Altf4ah/Modified-7-Level-PUC-Inverter-for-Photovoltaic-Applications/Arduino code/code.png

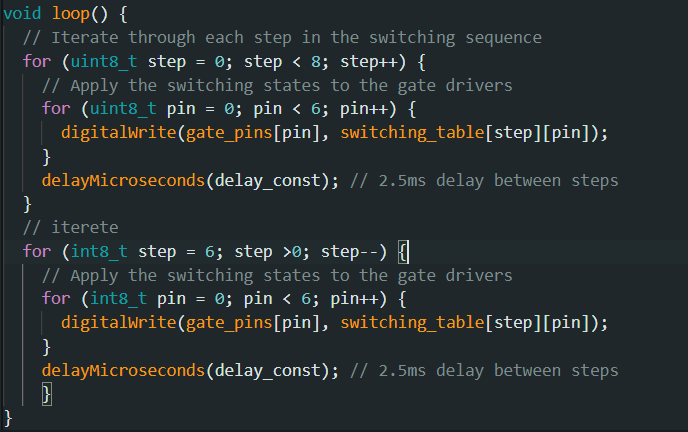
Arduino code/code.png
