Altf4ah/Modified-7-Level-PUC-Inverter-for-Photovoltaic-Applications/Arduino code/switching_table.png

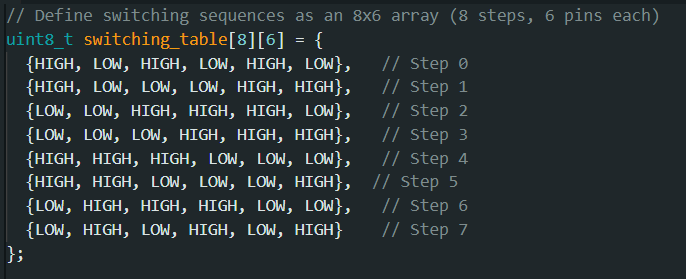
Arduino code/switching_table.png
