Altf4ah/Modified-7-Level-PUC-Inverter-for-Photovoltaic-Applications/Images/Circuit Diagrams/closedloop.jpg

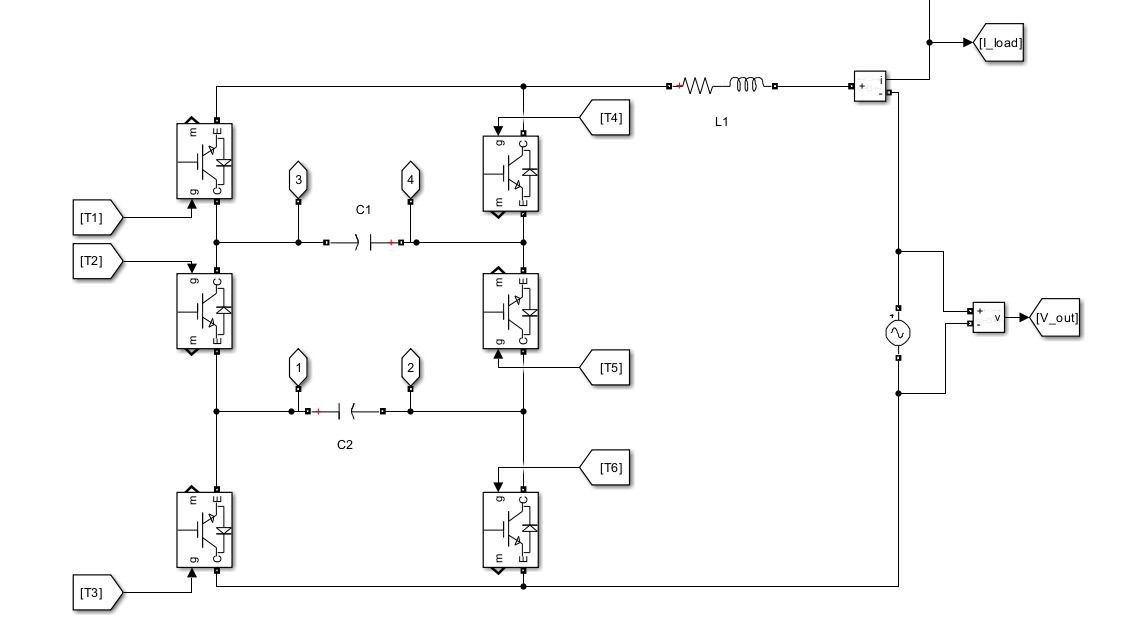
Images/Circuit Diagrams/closedloop.jpg
