Altf4ah/Modified-7-Level-PUC-Inverter-for-Photovoltaic-Applications/Images/Circuit Diagrams/driver_schematic.png

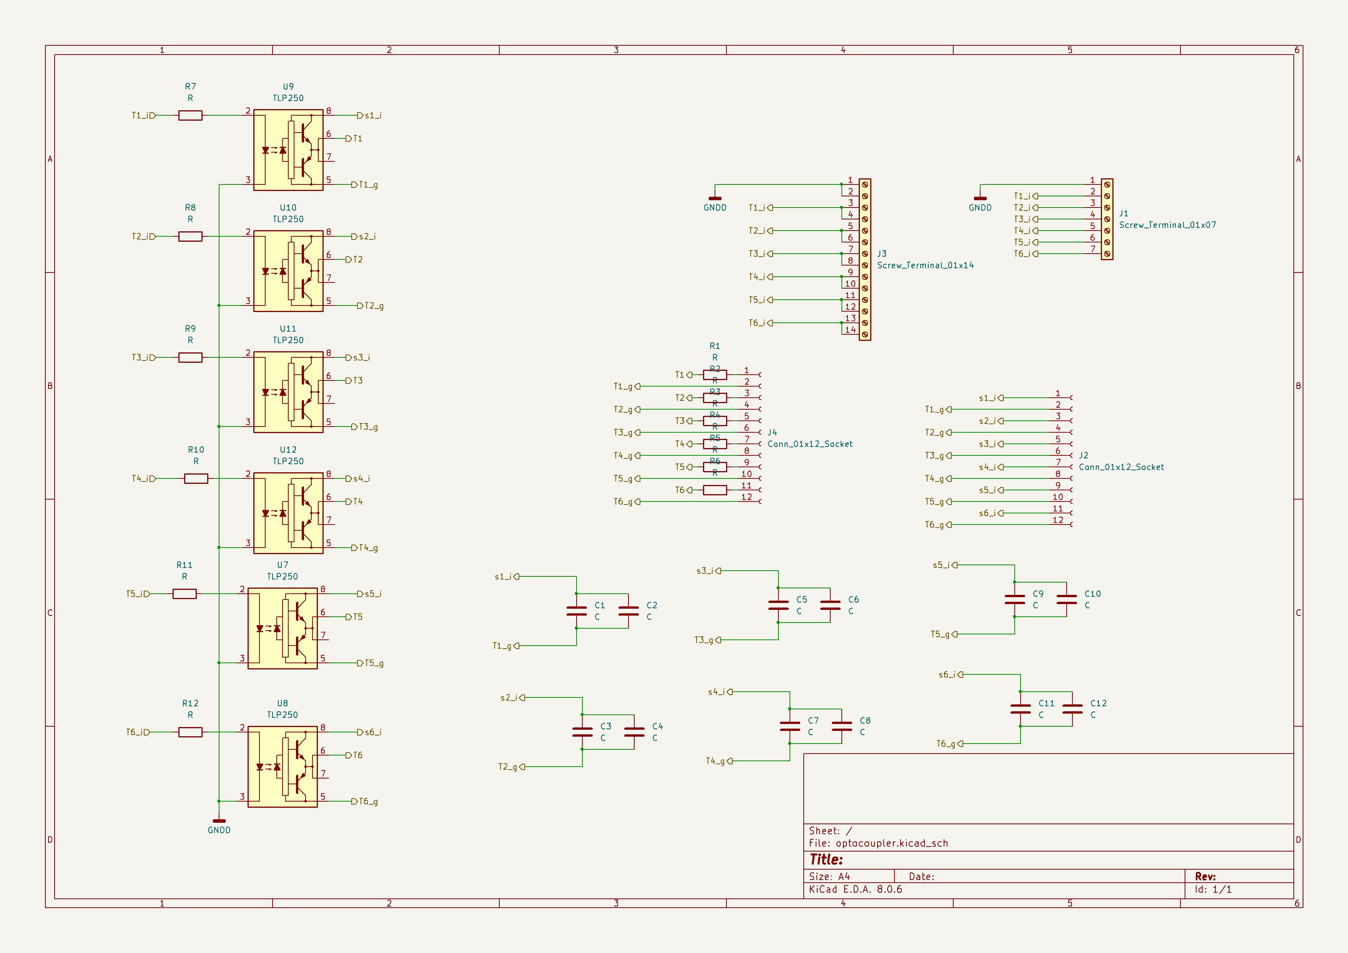
Images/Circuit Diagrams/driver_schematic.png
