Altf4ah/Modified-7-Level-PUC-Inverter-for-Photovoltaic-Applications/Images/Circuit Diagrams/Etching/etching1.jpg

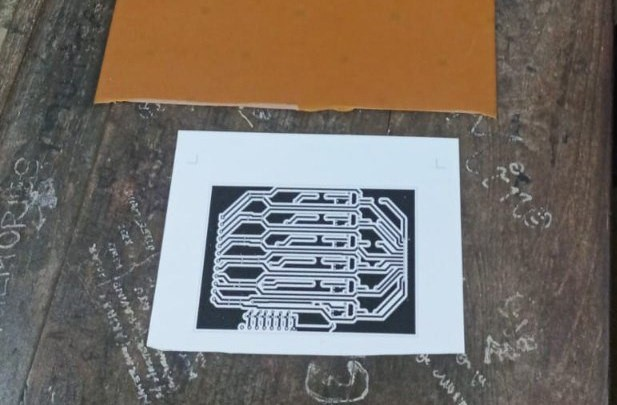
Images/Circuit Diagrams/Etching/etching1.jpg
