Altf4ah/Modified-7-Level-PUC-Inverter-for-Photovoltaic-Applications/Images/Circuit Diagrams/Etching/etching3.jpg

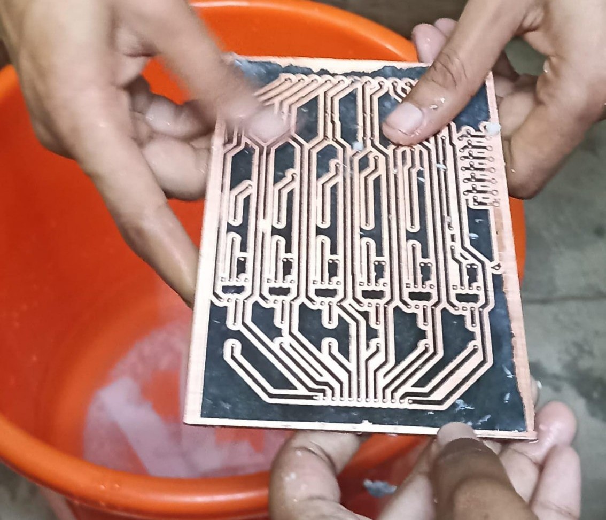
Images/Circuit Diagrams/Etching/etching3.jpg
