Altf4ah/Modified-7-Level-PUC-Inverter-for-Photovoltaic-Applications/Images/Circuit Diagrams/fb.jpg

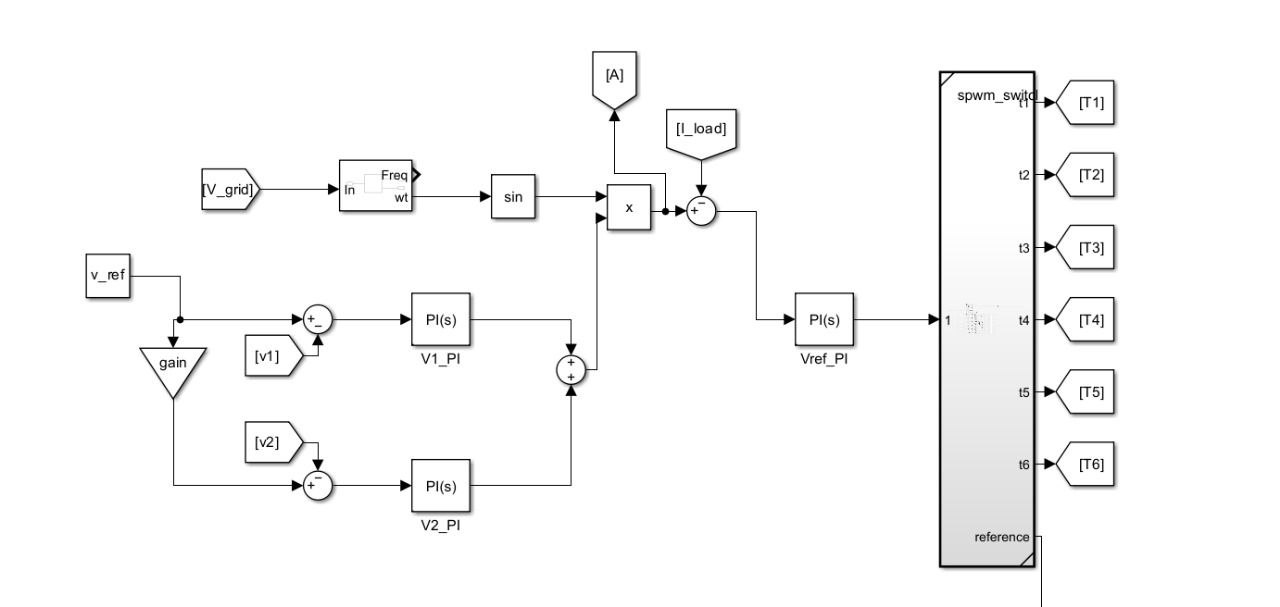
Images/Circuit Diagrams/fb.jpg
