Altf4ah/Modified-7-Level-PUC-Inverter-for-Photovoltaic-Applications/Images/Circuit Diagrams/inverter.png

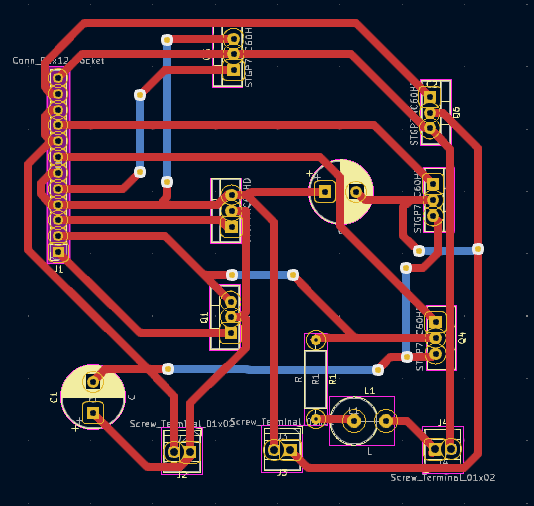
Images/Circuit Diagrams/inverter.png
