Altf4ah/Modified-7-Level-PUC-Inverter-for-Photovoltaic-Applications/Images/Circuit Diagrams/mpuc.png

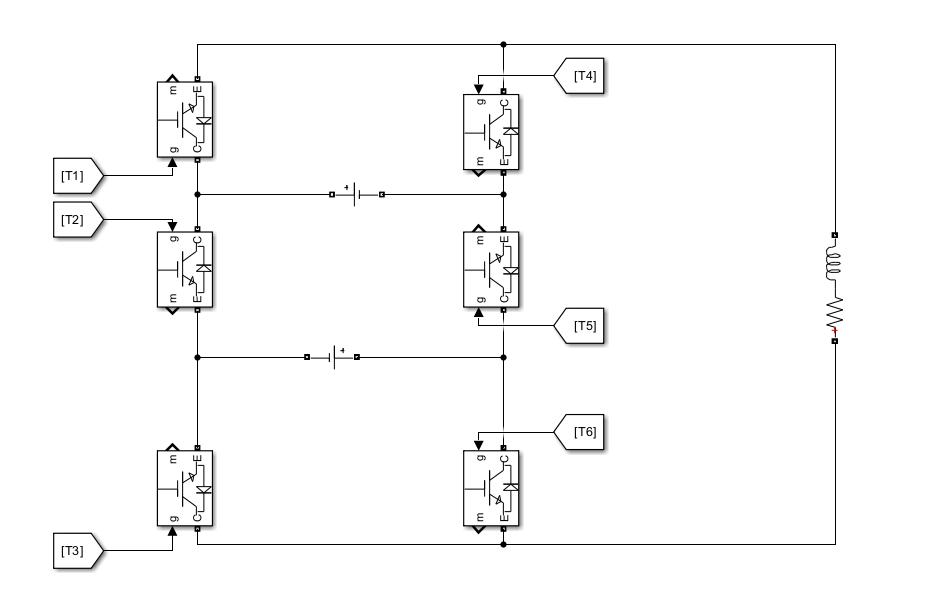
Images/Circuit Diagrams/mpuc.png
