Altf4ah/Modified-7-Level-PUC-Inverter-for-Photovoltaic-Applications/Images/Circuit Diagrams/openloop_diag.jpg

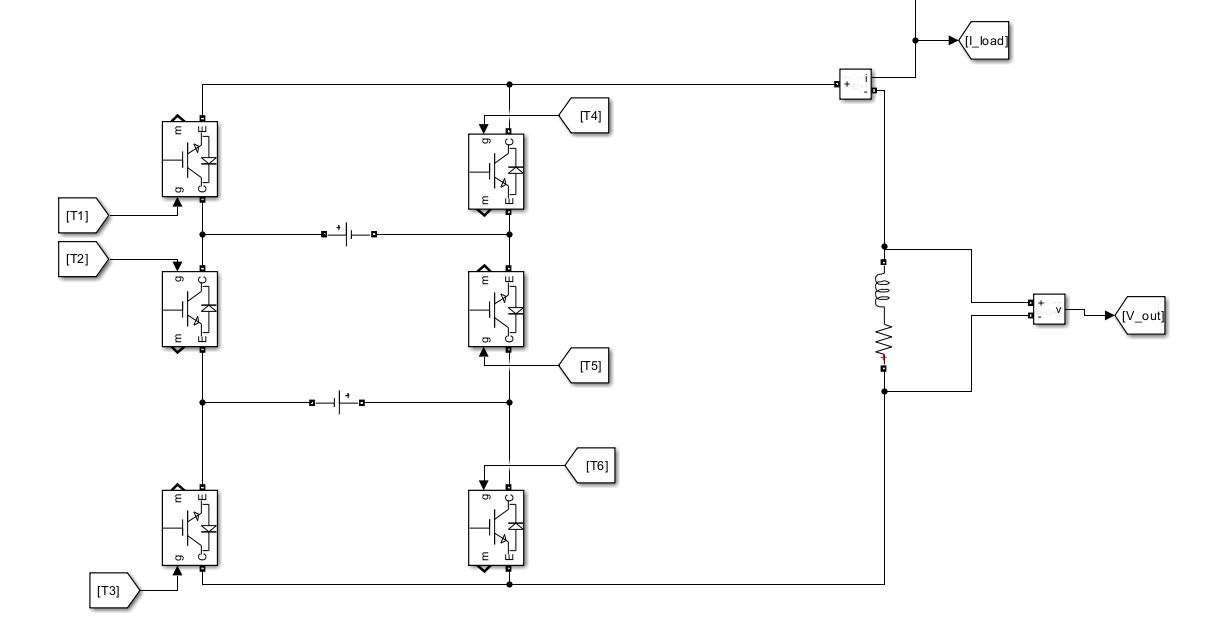
Images/Circuit Diagrams/openloop_diag.jpg
