Altf4ah/Modified-7-Level-PUC-Inverter-for-Photovoltaic-Applications/Images/Circuit Diagrams/opto.png

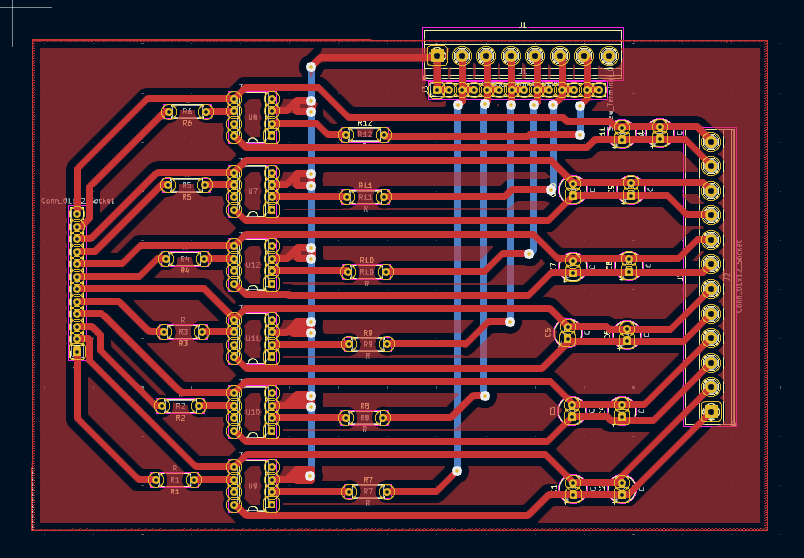
Images/Circuit Diagrams/opto.png
