Altf4ah/Modified-7-Level-PUC-Inverter-for-Photovoltaic-Applications/Images/Circuit Diagrams/PCB.png

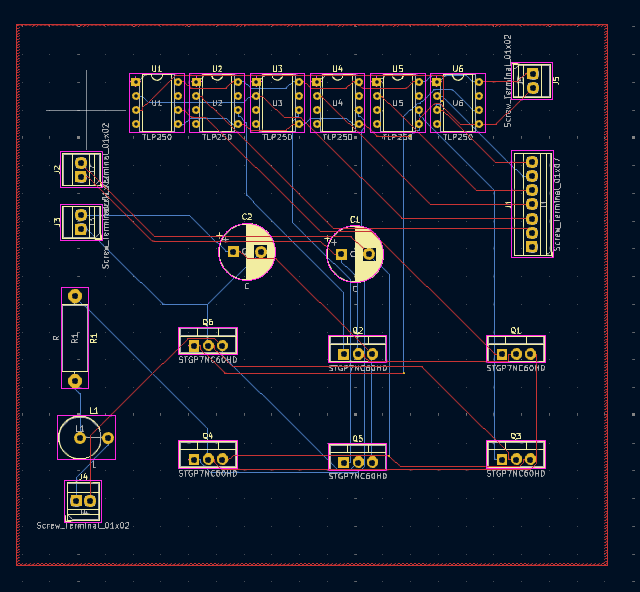
Images/Circuit Diagrams/PCB.png
