Altf4ah/Modified-7-Level-PUC-Inverter-for-Photovoltaic-Applications/Images/Circuit Diagrams/pcd.png

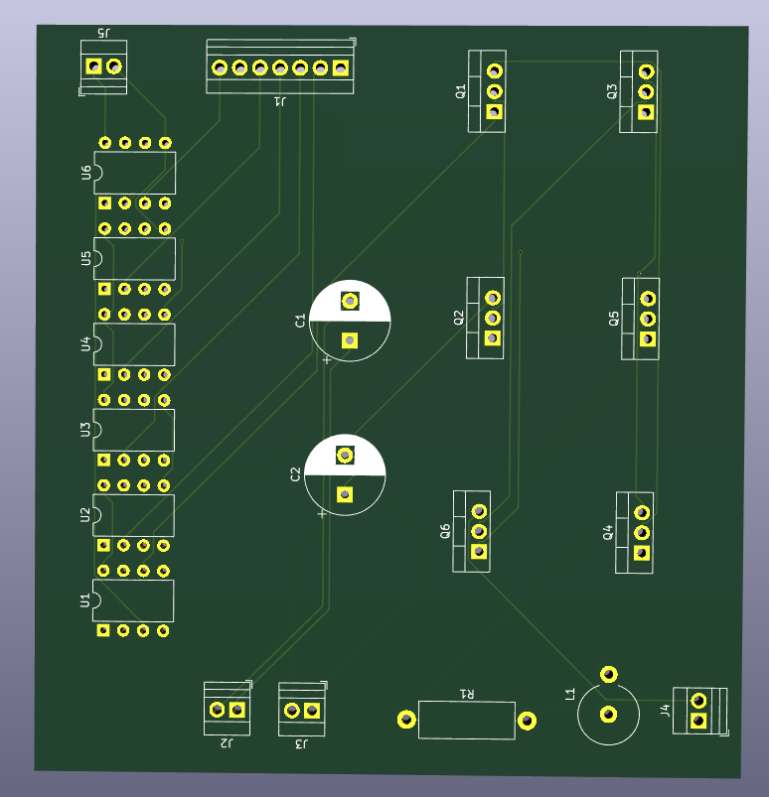
Images/Circuit Diagrams/pcd.png
