Altf4ah/Modified-7-Level-PUC-Inverter-for-Photovoltaic-Applications/Images/Circuit Diagrams/spwm.png

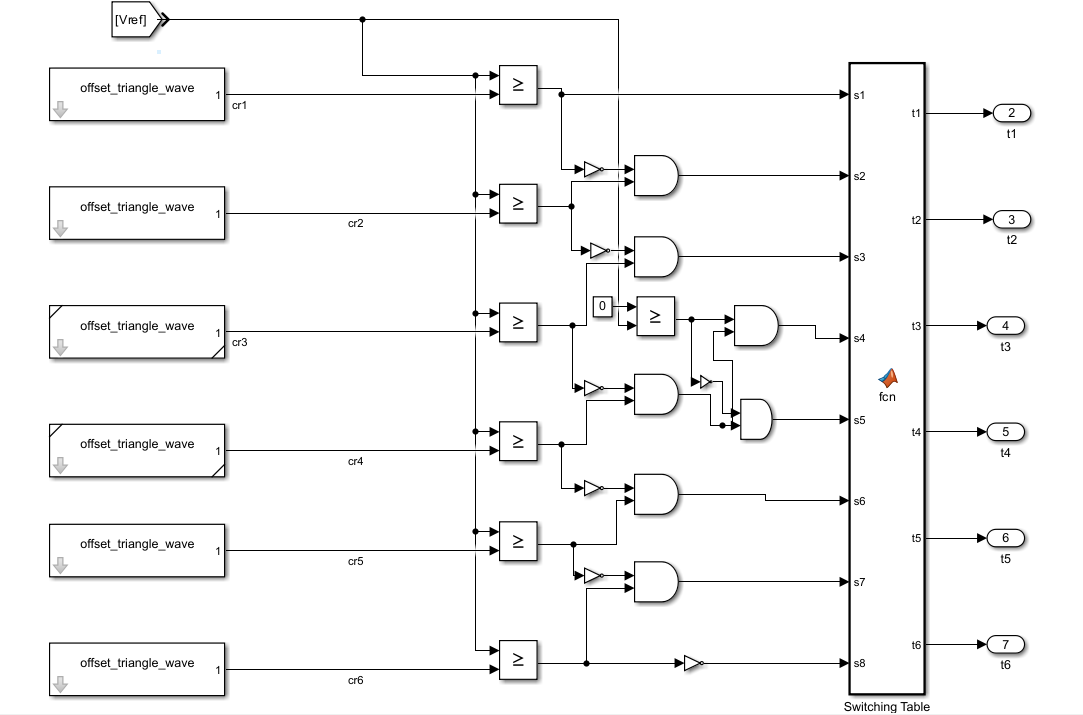
Images/Circuit Diagrams/spwm.png
