Altf4ah/Modified-7-Level-PUC-Inverter-for-Photovoltaic-Applications/Images/Hardware output waveform/out2.jpg

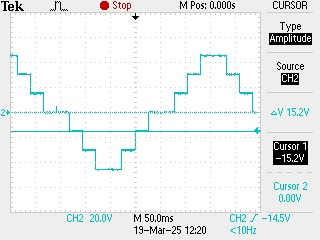
Images/Hardware output waveform/out2.jpg
