Altf4ah/Modified-7-Level-PUC-Inverter-for-Photovoltaic-Applications/Images/Simulation result/thd.jpg

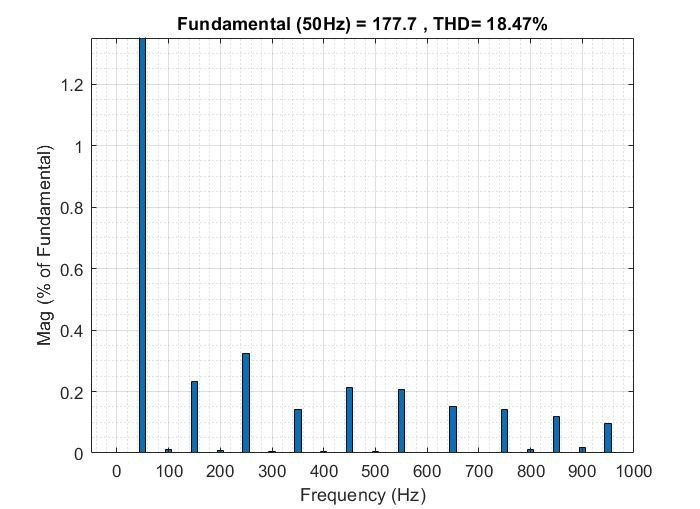
Images/Simulation result/thd.jpg
